kintsugi-computer/AT28C256Programmer/KiCad/AT28C256Programmer.kicad_sch

## KiCad design KiCad/AT28C256Programmer.kicad_sch (2024-10-19)

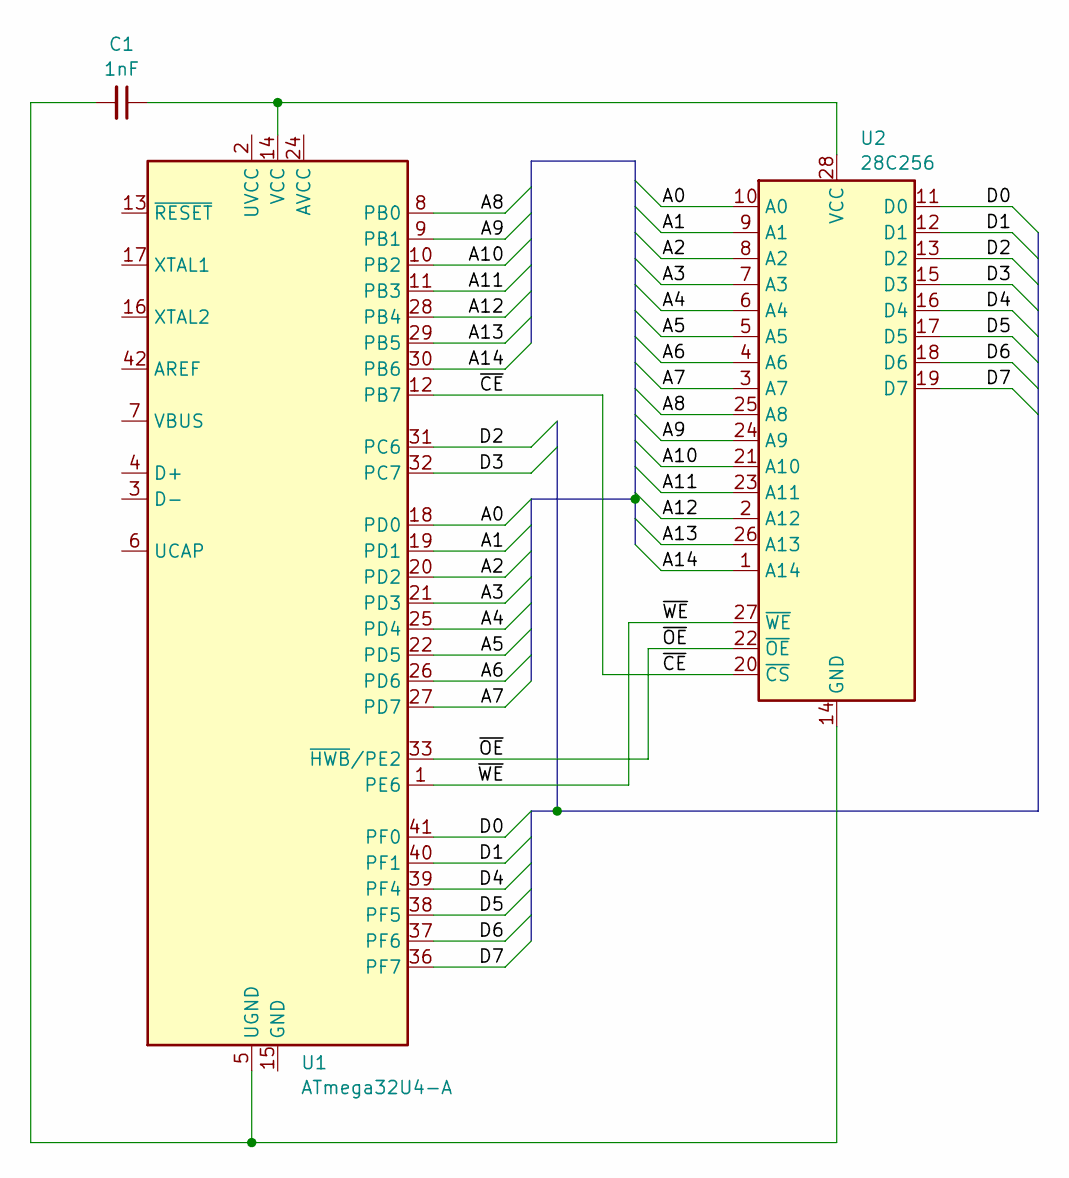
[picture p4: schematic AT28C256Programmer.kicad_sch]

Parts:
C1: 1nF
U1: ATmega32U4-A; TQFP-44_10x10mm_P0.8mm
U2: 28C256

Connections:
A0: U1.18 (PD0), U2.10 (A0)
A1: U1.19 (PD1), U2.9 (A1)
A2: U1.20 (PD2), U2.8 (A2)
A3: U1.21 (PD3), U2.7 (A3)
A4: U1.25 (PD4), U2.6 (A4)
A5: U1.22 (PD5), U2.5 (A5)
A6: U1.26 (PD6), U2.4 (A6)
A7: U1.27 (PD7), U2.3 (A7)
A8: U1.8 (PB0), U2.25 (A8)
A9: U1.9 (PB1), U2.24 (A9)
A10: U1.10 (PB2), U2.21 (A10)
A11: U1.11 (PB3), U2.23 (A11)
A12: U1.28 (PB4), U2.2 (A12)
A13: U1.29 (PB5), U2.26 (A13)
A14: U1.30 (PB6), U2.1 (A14)
D0: U1.41 (PF0), U2.11 (D0)
D1: U1.40 (PF1), U2.12 (D1)
D2: U1.31 (PC6), U2.13 (D2)
D3: U1.32 (PC7), U2.15 (D3)
D4: U1.39 (PF4), U2.16 (D4)
D5: U1.38 (PF5), U2.17 (D5)
D6: U1.37 (PF6), U2.18 (D6)
D7: U1.36 (PF7), U2.19 (D7)
unnamed: C1.1, U1.14 (VCC), U1.34 (VCC), U2.28 (VCC)
unnamed: C1.2, U1.5 (UGND), U2.14 (GND)
unnamed: U1.15 (GND), U1.23 (GND), U1.35 (GND), U1.43 (GND)
unnamed: U1.24 (AVCC), U1.44 (AVCC)
~CE: U1.12 (PB7), U2.20 (~CS)
~OE: U1.33 (~HWB/PE2), U2.22 (~OE)
~WE: U1.1 (PE6), U2.27 (~WE)
